jtsiomb/m68kcomputer/testprog/rtc/src/tctl.h

#ifndef TCTL_H_
#define TCTL_H_

#define TCTL_HOME		"\033[0G"
#define TCTL_KILL_END	"\033[K"
#define TCTL_KILL_HOME	("\033[1K" TCTL_HOME)
#define TCTL_CUR_SAVE	"\033[s"
#define TCTL_CUR_UNSAVE	"\033[u"

#endif	/* TCTL_H_ */
